Voxtercin/SecurityNode/assets/pcb.png

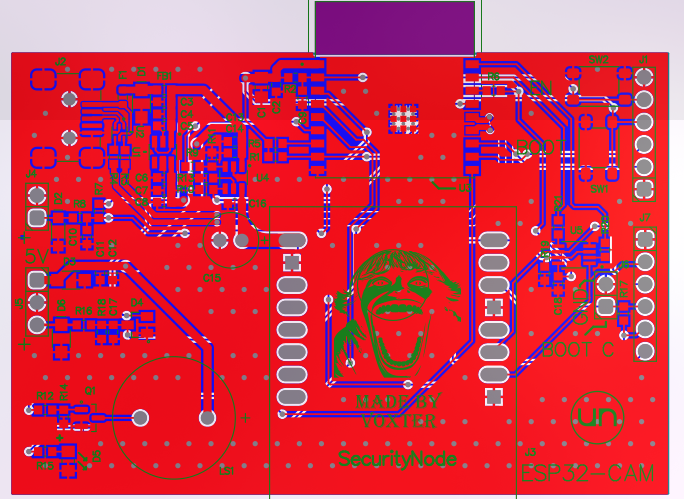
assets/pcb.png
