Voxtercin/SecurityNode/docs/presentation/images/pcb_above.png

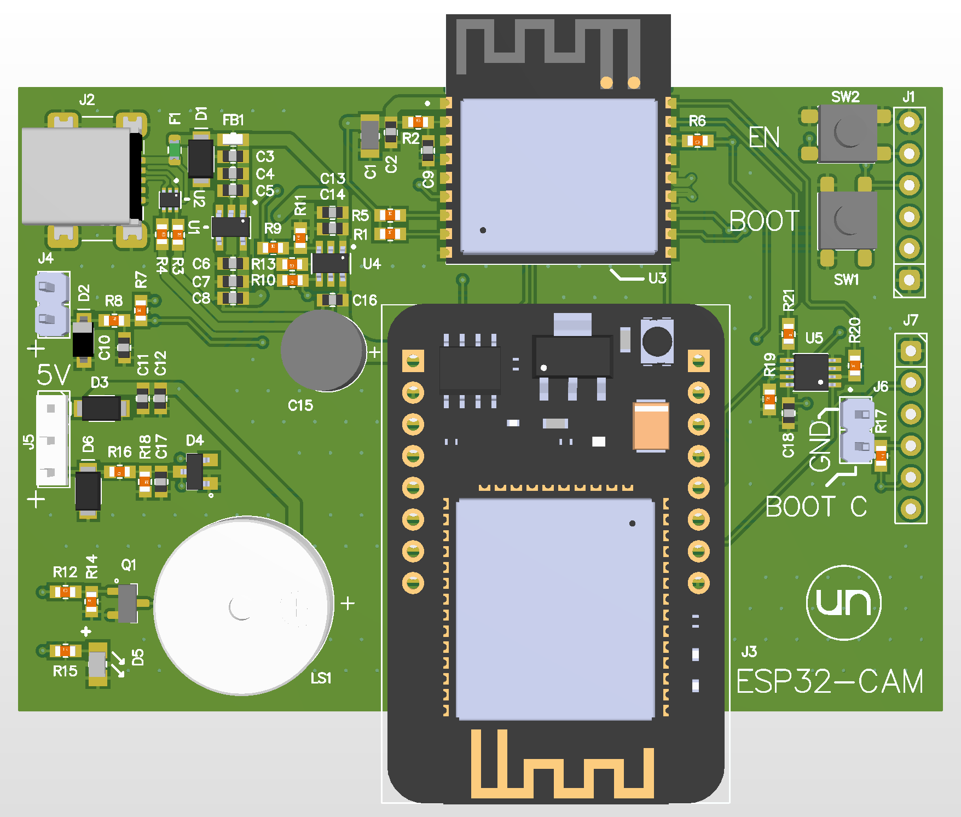
docs/presentation/images/pcb_above.png
