Voxtercin/SecurityNode/docs/presentation/images/pcb_below.png

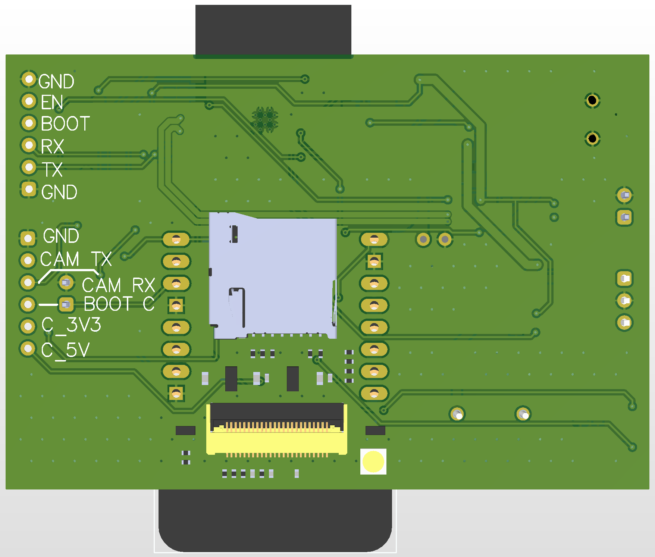
docs/presentation/images/pcb_below.png
